tumesh007/Shaving-Bowl/renders/02-top.png

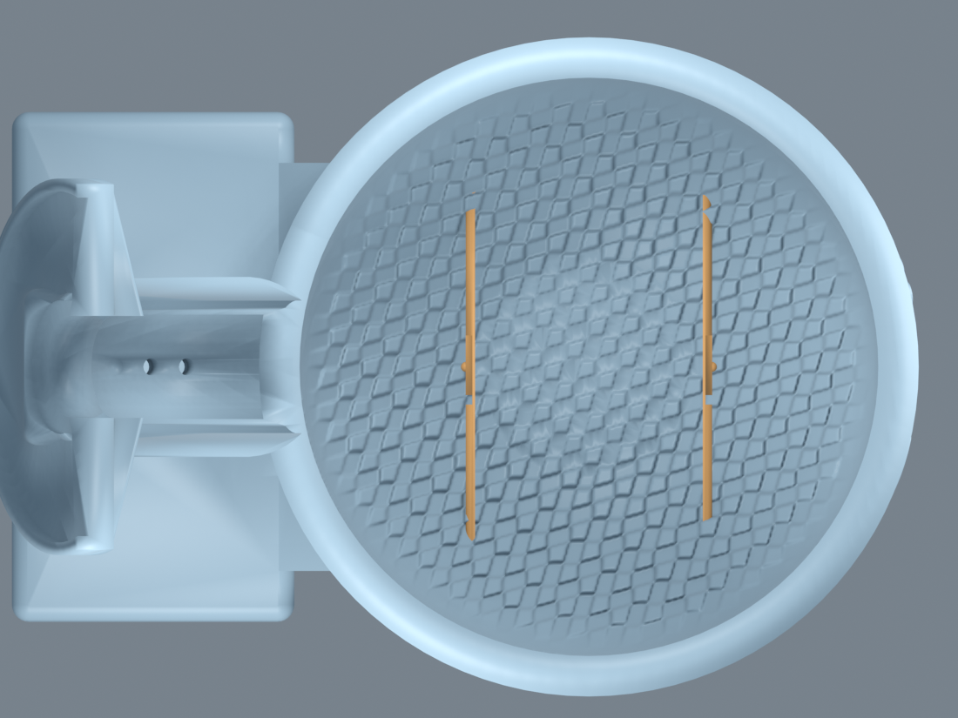
renders/02-top.png
