tumesh007/Shaving-Bowl/renders/03-side.png

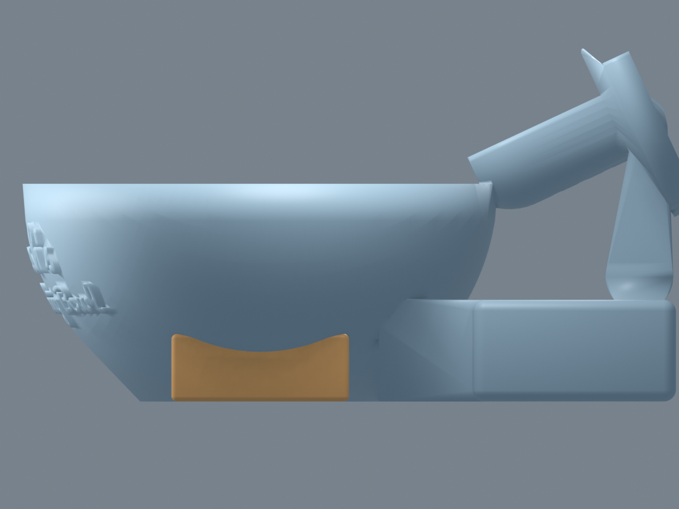
renders/03-side.png
