tumesh007/Shaving-Bowl/renders/06-texture-section.png

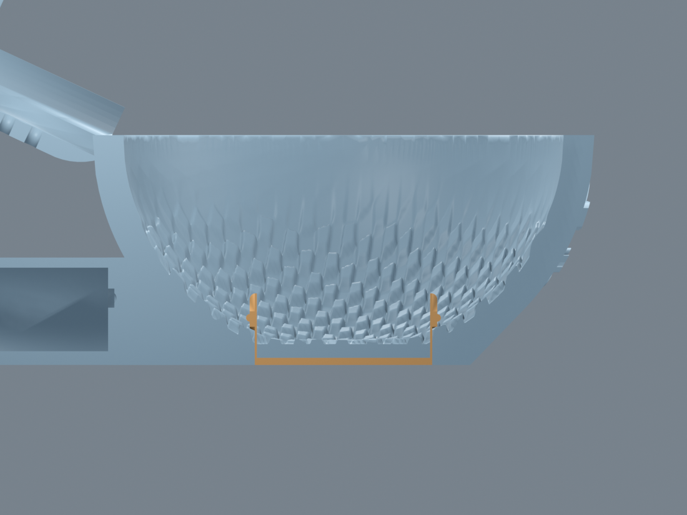
renders/06-texture-section.png
